JSa1987/ESPHome-HT-SLink/Schematics/HT_Controller.kicad_sch

## KiCad design Schematics/HT_Controller.kicad_sch (2025-07-17)

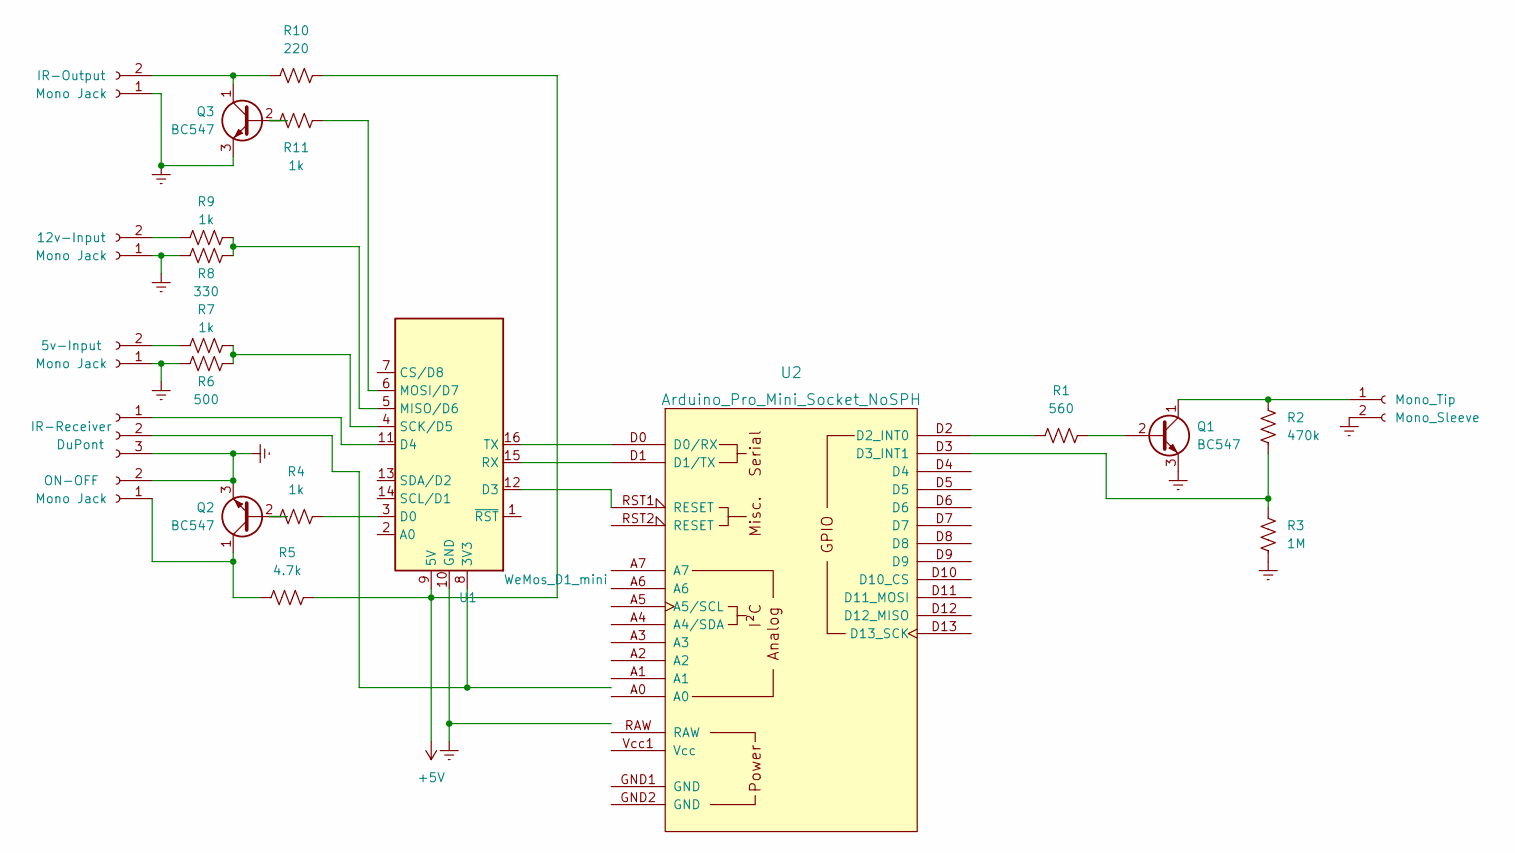
[picture p2: schematic HT_Controller.kicad_sch]

Parts:
5v-Input, 12v-Input: Mono Jack
IR-Output: Mono Jack
IR-Receiver: DuPont
Mono_Tip: Mono_Sleeve
ON-OFF: Mono Jack
Q1, Q2, Q3: BC547; TO-92_Inline
R1: 560
R2: 470k
R3: 1M
R4, R7, R9, R11: 1k
R5: 4.7k
R6: 500
R8: 330
R10: 220
U1: WeMos_D1_mini; WEMOS_D1_mini_light
U2: Arduino_Pro_Mini_Socket_NoSPH

Connections:
unnamed: 5v-Input.1, R6.1
unnamed: 5v-Input.2, R7.1
unnamed: 12v-Input.1, R8.1
unnamed: 12v-Input.2, R9.1
unnamed: IR-Output.1, Q3.3 (E)
unnamed: IR-Output.2, Q3.1 (C), R10.1
unnamed: IR-Receiver.1, U1.11 (D4)
unnamed: IR-Receiver.2, U1.8 (3V3)
unnamed: IR-Receiver.3, ON-OFF.2, Q2.3 (E)
unnamed: Mono_Tip.1, Q1.1 (C), R2.1
unnamed: ON-OFF.1, Q2.1 (C), R5.1
unnamed: Q1.2 (B), R1.2
unnamed: Q2.2 (B), R4.1
unnamed: Q3.2 (B), R11.1
unnamed: R1.1, U2.D2 (D2_INT0)
unnamed: R2.2, R3.1, U2.D3 (D3_INT1)
unnamed: R4.2, U1.3 (D0)
unnamed: R6.2, R7.2, U1.4 (SCK/D5)
unnamed: R8.2, R9.2, U1.5 (MISO/D6)
unnamed: R5.2, R10.2, U1.9 (5V)
unnamed: R11.2, U1.6 (MOSI/D7)
unnamed: U1.12 (D3), U2.RST1 (RESET)
unnamed: U1.15 (RX), U2.D1 (D1/TX)
unnamed: U1.16 (TX), U2.D0 (D0/RX)
